BoujeeEnjinia1701/curbcount/cad/drawings/CBC-DWG-101.pdf

### BUILD PLAN SKETCH, PLAN NOT YET BUILT CurbCount · github.com/BoujeeEnjinia1701/curbcount

FRONT VIEW
Scale 1:5; looking at the front (along +Y)

TOP VIEW
Scale 1:5; looking down (along -Z)

RIGHT VIEW
Scale 1:5; looking at the right side (along -X)

160

3 300

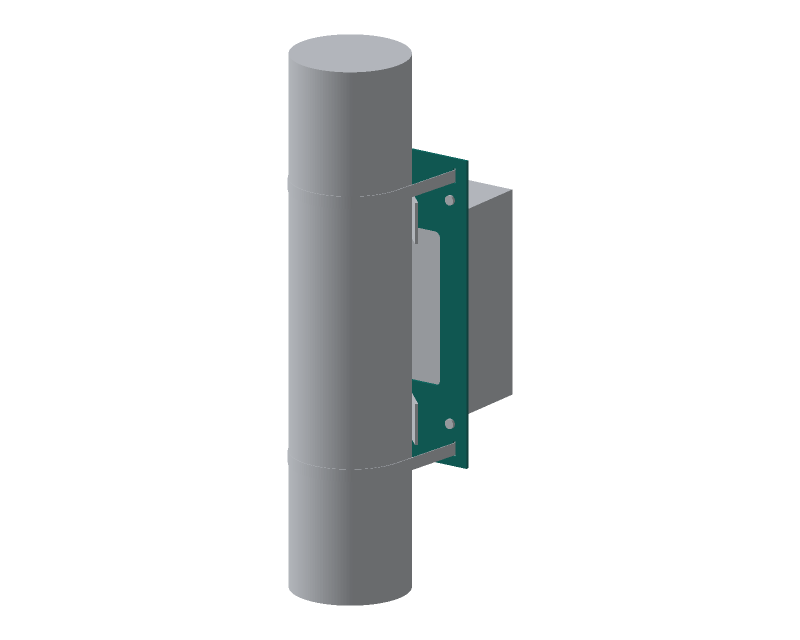
[picture p7: figure]

WHERE IT GOES
This part in colour, its neighbours in grey

HOW TO MAKE IT AND HOW IT FITS
Blank 160 x 300 mm, 3 mm aluminium. Front view is the face the box sits on. Heights from the bottom edge; sideways from the centre line.
Window 100 x 150 mm, 6 mm corners, 75 to 225 mm up: drill the corners 12 mm, cut between with a jigsaw, file straight. It saves weight.
Band slots 3 x 15 mm at 66 mm each side, centred 17 and 283 mm up: chain drill 3 mm and file square. The bands pass through these.
Lug screws 5.5 mm at 62 mm each side, 41 and 259 mm up.
V-saddle screws 4.5 mm on the centre line, 42, 62, 238 and 258 mm up; countersink from the front so the screw heads sit flush.
Deburr every hole and edge; round the corners to about 2 mm.
Fit: V-saddles on the back, the enclosure on the front between the bands; each band crosses the front above or below the box. Check: lay the saddles and lugs on it and look through each hole.
REV | DESCRIPTION | DATE | BY
P1 | Making sketch for the prototype build plan | 2026-10-02 | AC
CURBCOUNT | github.com/BoujeeEnjinia1701/curbcount

## CurbCount enclosure saddle plate: making sketch

DRAWING NO.
CBC-DWG-101

REV
P1

SHEET
1 of 1

SIZE

## ANSI B

SCALE
1:5

UNITS
mm
PROJECTION | DATE
2026-10-02

DRAWN
Amish Chadha

MATERIAL / NOTES
Aluminium sheet 3 mm, 5052 or 6061 class
Licensed CERN-OHL-S-2.0 · Design Molecule Lab · designmolecule.com | Generated from cad/src; do not edit by hand
