BoujeeEnjinia1701/curbcount/cad/drawings/CBC-DWG-102.pdf

### BUILD PLAN SKETCH, PLAN NOT YET BUILT CurbCount · github.com/BoujeeEnjinia1701/curbcount

FRONT VIEW
Scale 1:2; looking at the front (along +Y)

TOP VIEW
Scale 1:2; looking down (along -Z)

RIGHT VIEW
Scale 1:2; looking at the right side (along -X)

49

116 40

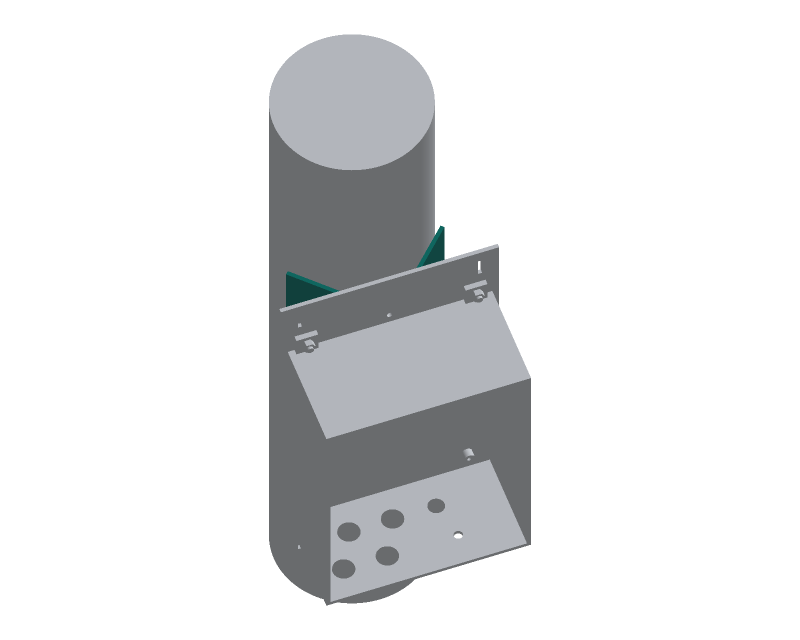
[picture p8: figure]

WHERE IT GOES
This part in colour, its neighbours in grey

HOW TO MAKE IT AND HOW IT FITS
Make four, all the same: two for the enclosure plate, two for the arm plate. Blank 150 x 40 mm of 3 mm sheet: a 20 mm flat in the middle and a
65 mm wing each side. Scribe the two bend lines 10 mm each side
of the centre line.
Bend each wing 45 degrees in a vice with soft jaws, inside radius about 3 mm, so the two wings meet at 90 degrees (the V).
Two holes on the centre line of the flat, 10 mm each side of the middle: drill 3.3 mm and tap M4. File the screw tails flush later. Fit: the flat sits on the back of a saddle plate, the V opens toward the pole; two M4 countersunk screws from the plate's front.
The 114 mm pole touches both wings 43 mm out from the bends; 60 to 140 mm poles also seat on both wings.
Check: both wings at 45 degrees to the flat, within 1 degree.
REV | DESCRIPTION | DATE | BY
P1 | Making sketch for the prototype build plan | 2026-10-02 | AC
CURBCOUNT | github.com/BoujeeEnjinia1701/curbcount

## CurbCount V-saddle (make 4): making sketch

DRAWING NO.
CBC-DWG-102

REV
P1

SHEET
1 of 1

SIZE

## ANSI B

SCALE
1:2

UNITS
mm
PROJECTION | DATE
2026-10-02

DRAWN
Amish Chadha

MATERIAL / NOTES
Aluminium sheet 3 mm, 5052-H32 (bends cold)
Licensed CERN-OHL-S-2.0 · Design Molecule Lab · designmolecule.com | Generated from cad/src; do not edit by hand
