BoujeeEnjinia1701/curbcount/cad/drawings/CBC-DWG-103.pdf

### BUILD PLAN SKETCH, PLAN NOT YET BUILT CurbCount · github.com/BoujeeEnjinia1701/curbcount

FRONT VIEW
Scale 1:5; looking at the front (along +Y)

TOP VIEW
Scale 1:5; looking down (along -Z)

RIGHT VIEW
Scale 1:5; looking at the right side (along -X)

78

150 208

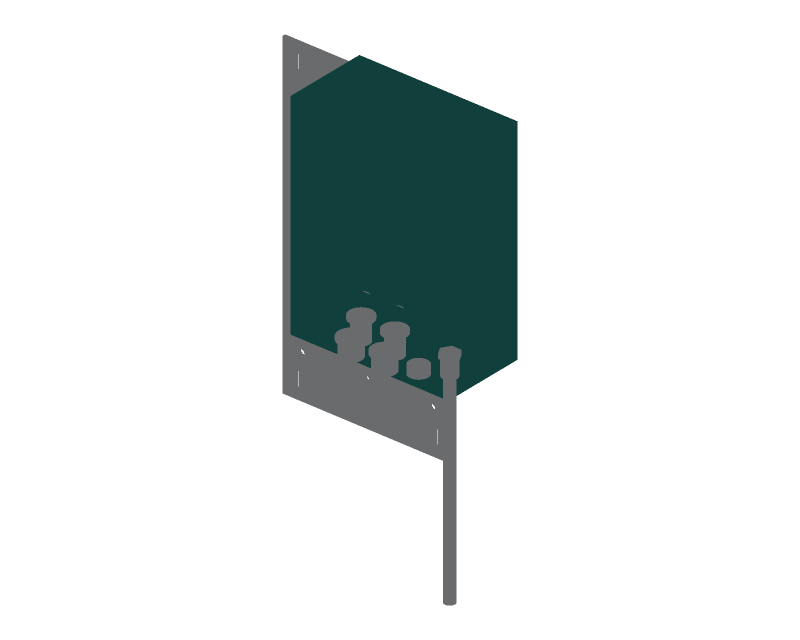
[picture p9: figure]

WHERE IT GOES
This part in colour, its neighbours in grey

HOW TO MAKE IT AND HOW IT FITS
The FieldNode enclosure, drilled exactly as FieldNode's build plan says. Drawn upside down: stand the box on its top, back face toward you. Back row, 27 mm from the back face: gland 1 at 40 left, gland 2 at
8 left (16.2 mm holes), vent at 24 right (12.2 mm).
Front row, 55 mm from the back face: port A at 54 left, port B at
22 left (16.2 mm), antenna at 30 right (6.5 mm).
Left and right as seen from the front (the lid).
Tape the face, pilot drill 3 mm slowly with wood behind, open out with a step drill. No solvents: polycarbonate crazes.
Fit the maker's four lugs at the back corners.
In CurbCount, gland 1 takes the panel lead and port A the sensor cable; gland 2 is plugged and port B capped.
REV | DESCRIPTION | DATE | BY
P1 | Making sketch for the prototype build plan | 2026-10-02 | AC
CURBCOUNT | github.com/BoujeeEnjinia1701/curbcount

## CurbCount FieldNode enclosure: drilling sketch

DRAWING NO.
CBC-DWG-103

REV
P1

SHEET
1 of 1

SIZE

## ANSI B

SCALE
1:5

UNITS
mm
PROJECTION | DATE
2026-10-02

DRAWN
Amish Chadha

MATERIAL / NOTES
Bought IP65 polycarbonate box 150 x 90 x 200 mm
Licensed CERN-OHL-S-2.0 · Design Molecule Lab · designmolecule.com | Generated from cad/src; do not edit by hand
