BoujeeEnjinia1701/curbcount/cad/drawings/CBC-DWG-104.pdf

### BUILD PLAN SKETCH, PLAN NOT YET BUILT CurbCount · github.com/BoujeeEnjinia1701/curbcount

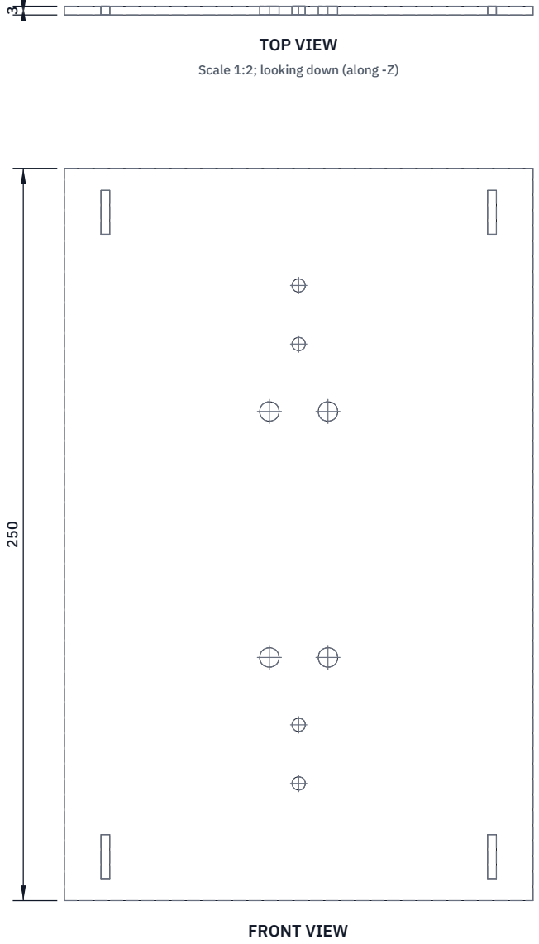
[picture p10: figure]
FRONT VIEW; TOP VIEW; Scale 1:2; looking down (along -Z)

Scale 1:2; looking at the front (along +Y)

RIGHT VIEW
Scale 1:2; looking at the right side (along -X)

160

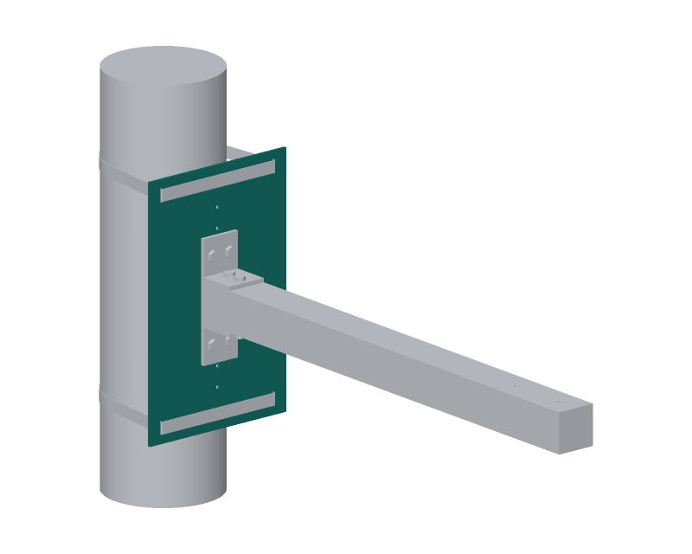
[picture p11: figure]

WHERE IT GOES
This part in colour, its neighbours in grey

HOW TO MAKE IT AND HOW IT FITS
Blank 160 x 250 mm, 3 mm aluminium. Front view is the face the arm butts against. Heights from the bottom edge; sideways from the centre. Band slots 3 x 15 mm at 66 mm each side, centred 15 and 235 mm up: chain drill 3 mm and file square.
Bracket bolts 6.6 mm at 10 mm each side, 83 and 167 mm up. V-saddle screws 4.5 mm on the centre line, 40, 60, 190 and 210 mm up; countersink from the front.
Deburr every hole; round the corners to about 2 mm.
Fit: V-saddles on the back; the arm tube butts the front at mid
height, held by the two brackets; the bands cross the front above and below the brackets.
Check: offer the brackets up and look through the bolt holes.
REV | DESCRIPTION | DATE | BY
P1 | Making sketch for the prototype build plan | 2026-10-02 | AC
CURBCOUNT | github.com/BoujeeEnjinia1701/curbcount

## CurbCount arm saddle plate: making sketch

DRAWING NO.
CBC-DWG-104

REV
P1

SHEET
1 of 1

SIZE

## ANSI B

SCALE
1:2

UNITS
mm
PROJECTION | DATE
2026-10-02

DRAWN
Amish Chadha

MATERIAL / NOTES
Aluminium sheet 3 mm, 5052 or 6061 class
Licensed CERN-OHL-S-2.0 · Design Molecule Lab · designmolecule.com | Generated from cad/src; do not edit by hand
