BoujeeEnjinia1701/curbcount/cad/drawings/CBC-DWG-105.pdf

### BUILD PLAN SKETCH, PLAN NOT YET BUILT CurbCount · github.com/BoujeeEnjinia1701/curbcount

FRONT VIEW
Scale 1:1; looking at the front (along +Y)

TOP VIEW
Scale 1:1; looking down (along -Z)

RIGHT VIEW
Scale 1:1; looking at the right side (along -X)

40

40 40

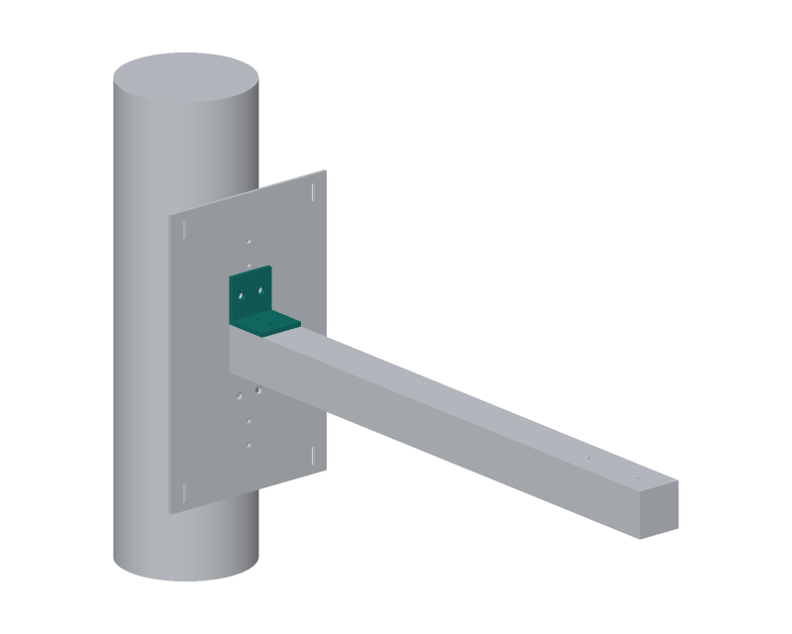
[picture p12: figure]

WHERE IT GOES
This part in colour, its neighbours in grey

HOW TO MAKE IT AND HOW IT FITS
Cut two 40 mm lengths of 40 x 40 x 4 angle; square and deburr. Upright leg (goes on the plate): two 6.6 mm holes 10 mm each side of the middle, 22 mm from the heel (the outside corner).
Flat leg (goes on the tube): two 6.6 mm holes on the middle line, 15 and 30 mm from the heel.
Both brackets are the same; one goes on top of the tube, the other underneath, upside down.
Fit: the upright leg on the plate's front, its heel at the tube's
top (or bottom) face; M6 bolts through the plate, nuts behind. Two M6 bolts go down through both brackets and the tube, each with a crush spacer inside the tube.
Check: the bracket sits flat on both the plate and the tube.
REV | DESCRIPTION | DATE | BY
P1 | Making sketch for the prototype build plan | 2026-10-02 | AC
CURBCOUNT | github.com/BoujeeEnjinia1701/curbcount

## CurbCount arm bracket (make 2): making sketch

DRAWING NO.
CBC-DWG-105

REV
P1

SHEET
1 of 1

SIZE

## ANSI B

SCALE
1:1

UNITS
mm
PROJECTION | DATE
2026-10-02

DRAWN
Amish Chadha

MATERIAL / NOTES
Aluminium equal angle 40 x 40 x 4 mm
Licensed CERN-OHL-S-2.0 · Design Molecule Lab · designmolecule.com | Generated from cad/src; do not edit by hand
