BoujeeEnjinia1701/curbcount/cad/drawings/CBC-DWG-106.pdf

### BUILD PLAN SKETCH, PLAN NOT YET BUILT CurbCount · github.com/BoujeeEnjinia1701/curbcount

FRONT VIEW
Scale 1:5; looking at the front (along +Y)

TOP VIEW
Scale 1:5; looking down (along -Z)

RIGHT VIEW
Scale 1:5; looking at the right side (along -X)

498

40 40

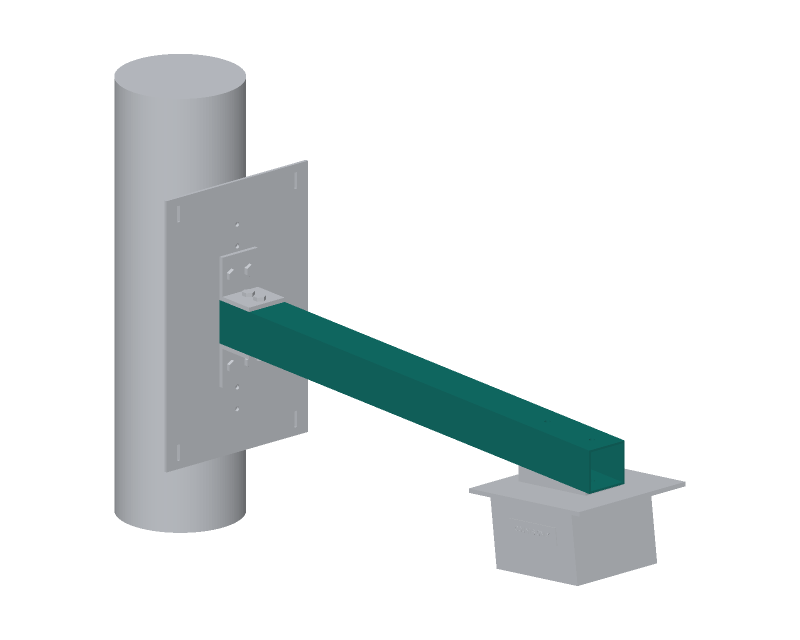
[picture p13: figure]

WHERE IT GOES
This part in colour, its neighbours in grey

HOW TO MAKE IT AND HOW IT FITS
Cut 498 mm of 40 x 40 x 2 tube; square both ends (the pole end must sit flat on the plate) and deburr.
Plate end: two 6.6 mm holes straight through top and bottom walls, on the centre line, 15 and 30 mm from the end.
Head end: two 5.5 mm holes straight through, on the centre line, 418 and 478 mm from the plate end.
Drill each pair square through both walls (drill press, V-block).
Cut four crush spacers 36 mm long from 10 mm aluminium tube; they sit inside the tube on the bolts so the walls do not crush.
Fit a plastic end cap in the head end.
Check: on a flat bench the tube does not rock; holes line up
top to bottom (a rod passes straight through).
REV | DESCRIPTION | DATE | BY
P1 | Making sketch for the prototype build plan | 2026-10-02 | AC
CURBCOUNT | github.com/BoujeeEnjinia1701/curbcount

## CurbCount arm tube: making sketch

DRAWING NO.
CBC-DWG-106

REV
P1

SHEET
1 of 1

SIZE

## ANSI B

SCALE
1:5

UNITS
mm
PROJECTION | DATE
2026-10-02

DRAWN
Amish Chadha

MATERIAL / NOTES
Aluminium square tube 40 x 40 x 2 mm, 6063
Licensed CERN-OHL-S-2.0 · Design Molecule Lab · designmolecule.com | Generated from cad/src; do not edit by hand
