BoujeeEnjinia1701/curbcount/cad/drawings/CBC-DWG-107.pdf

### BUILD PLAN SKETCH, PLAN NOT YET BUILT CurbCount · github.com/BoujeeEnjinia1701/curbcount

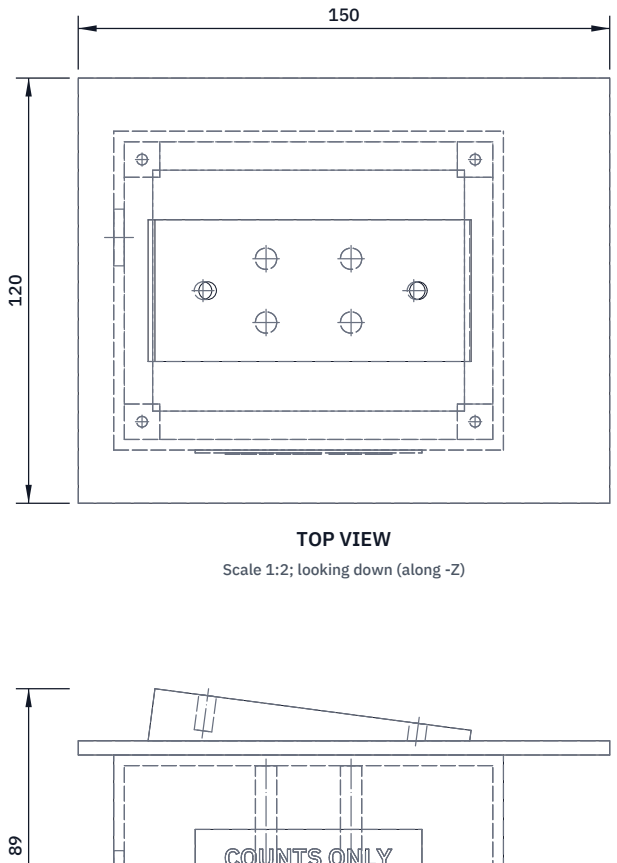
[picture p14: figure]
TOP VIEW; Scale 1:2; looking down (along -Z)

FRONT VIEW
Scale 1:2; looking at the front (along +Y)

RIGHT VIEW
Scale 1:2; looking at the right side (along -X)

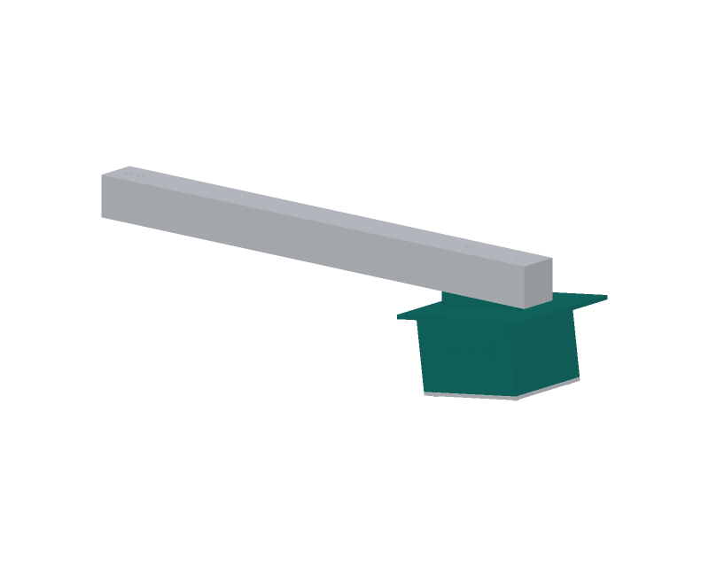
[picture p15: figure]

WHERE IT GOES
This part in colour, its neighbours in grey

HOW TO MAKE IT AND HOW IT FITS
Print in ASA in an enclosed printer, hood down on the bed; support the window ledge. Housing 110 x 90 x 70 mm, walls 3 mm,
hood 150 x 120 x 4 mm, set 10 mm toward the road side.
Ledge 8 mm wide inside the open bottom: the window clamps to it. Four corner bosses: press in M3 heat-set inserts, 47 and 37 mm each side of centre, from below.
Four standoffs from the roof carry the array breakout.
Wedge pad on the hood top: it makes the 7.5 degree tilt; its top is level under the arm. Press in two M5 heat-set inserts, 60 apart. End wall (pole side): 16.2 mm hole, 15 mm off centre, for the gland. Drill a 5 mm lanyard hole in the hood's road-side overhang. Road-side wall: a raised plaque 64 x 16 mm, 0.8 mm high, with COUNTS ONLY in 7 mm letters 0.4 mm higher, printed in the housing. Check: the wedge top is flat; the ledge face is flat for the film.
REV | DESCRIPTION | DATE | BY
P1 | Making sketch for the prototype build plan | 2026-10-02 | AC
CURBCOUNT | github.com/BoujeeEnjinia1701/curbcount

## CurbCount head housing: making sketch

DRAWING NO.
CBC-DWG-107

REV
P1

SHEET
1 of 1

SIZE

## ANSI B

SCALE
1:2

UNITS
mm
PROJECTION | DATE
2026-10-02

DRAWN
Amish Chadha

MATERIAL / NOTES
ASA, 3D printed, 4 perimeters, 40 % infill
Licensed CERN-OHL-S-2.0 · Design Molecule Lab · designmolecule.com | Generated from cad/src; do not edit by hand
