BoujeeEnjinia1701/curbcount/cad/drawings/CBC-DWG-108.pdf

### BUILD PLAN SKETCH, PLAN NOT YET BUILT CurbCount · github.com/BoujeeEnjinia1701/curbcount

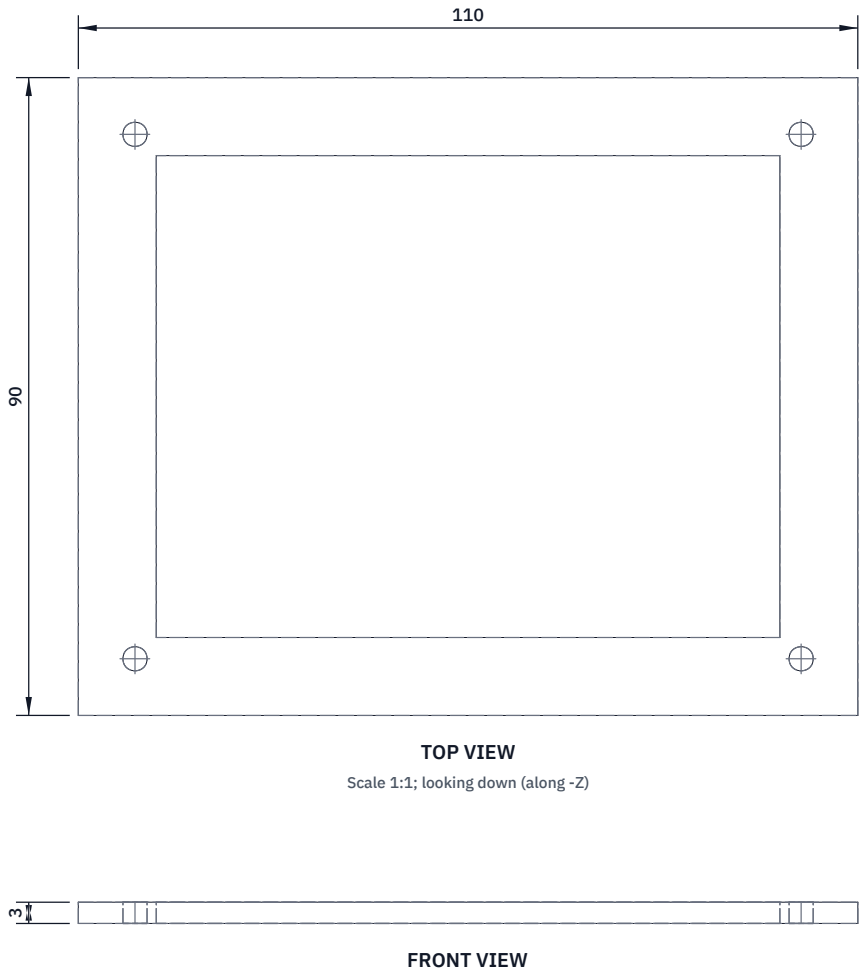
[picture p16: figure]
FRONT VIEW; TOP VIEW; Scale 1:1; looking down (along -Z)

Scale 1:1; looking at the front (along +Y)

RIGHT VIEW
Scale 1:1; looking at the right side (along -X)

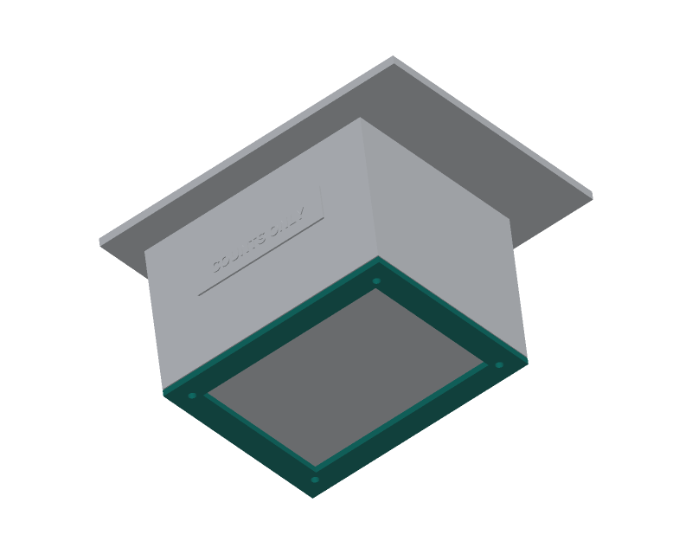
[picture p17: figure]

WHERE IT GOES
This part in colour, its neighbours in grey

HOW TO MAKE IT AND HOW IT FITS
Frame: print flat in ASA, 110 x 90 x 3 mm with an 88 x 68 mm opening and four 3.4 mm holes, 47 and 37 mm each side of centre.
Film: cut 100 x 80 mm from 0.5 mm unpigmented HDPE with a sharp knife on glass; do not touch the middle with bare fingers.
Use the frame as a template: punch four 3.5 mm holes in the film. Fit: film on the housing ledge, frame over it, four M3 screws into
the heat-set inserts, tightened evenly until the film is flat.
The array looks through the 88 x 68 mm opening; the field of view needs only about 30 x 20 mm of it.
Check: the film is flat and taut with no creases in the opening.
REV | DESCRIPTION | DATE | BY
P1 | Making sketch for the prototype build plan | 2026-10-02 | AC
CURBCOUNT | github.com/BoujeeEnjinia1701/curbcount

## CurbCount window frame and film: making sketch

DRAWING NO.
CBC-DWG-108

REV
P1

SHEET
1 of 1

SIZE

## ANSI B

SCALE
1:1

UNITS
mm
PROJECTION | DATE
2026-10-02

DRAWN
Amish Chadha

MATERIAL / NOTES
Frame ASA, 3D printed; film 0.5 mm HDPE
Licensed CERN-OHL-S-2.0 · Design Molecule Lab · designmolecule.com | Generated from cad/src; do not edit by hand
