BoujeeEnjinia1701/curbcount/cad/drawings/CBC-DWG-109.pdf

### BUILD PLAN SKETCH, PLAN NOT YET BUILT CurbCount · github.com/BoujeeEnjinia1701/curbcount

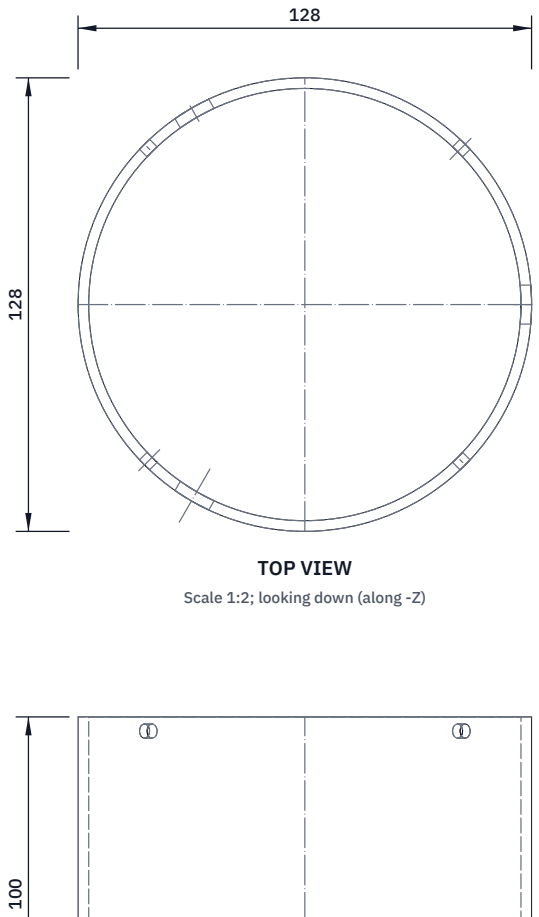
[picture p18: figure]
TOP VIEW; Scale 1:2; looking down (along -Z)

FRONT VIEW
Scale 1:2; looking at the front (along +Y)

RIGHT VIEW
Scale 1:2; looking at the right side (along -X)

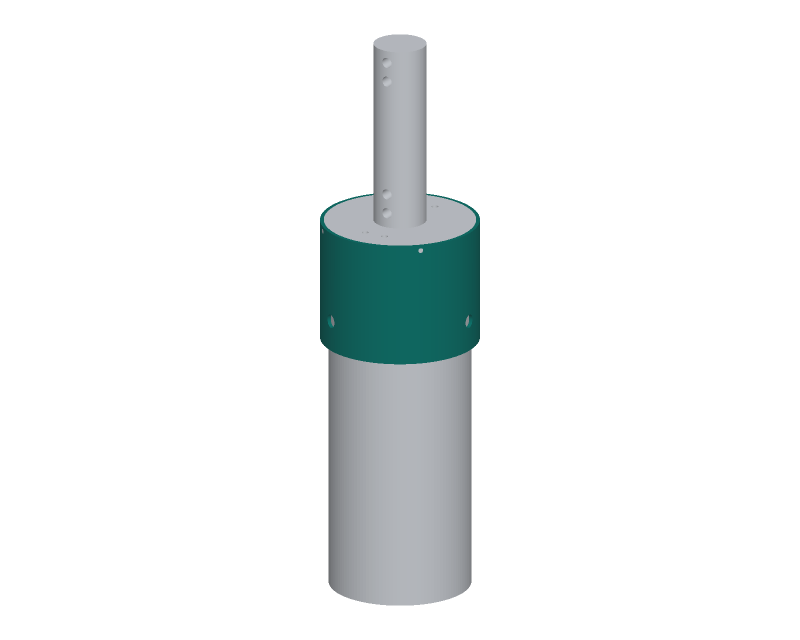
[picture p19: figure]

WHERE IT GOES
This part in colour, its neighbours in grey

HOW TO MAKE IT AND HOW IT FITS
Cut 100 mm of round tube; square and deburr both ends.
The bore must be 122 mm or more so it slides over a 114 mm pole. Top: four 4.5 mm holes 4 mm down from the top edge, at 45, 135, 225 and 315 degrees; countersink them for M4 screws.
Bottom: three 11 mm holes 25 mm up from the bottom edge, at 0, 120 and 240 degrees; set an M8 stainless rivet nut in each.
Put the hole at 0 degrees on the road side when fitting.
Fit: the cap disc goes inside the top, flush, on the four radial
screws; the sleeve then sits on the pole top through the disc.
Three M8 cup-point set screws in the rivet nuts centre it on the pole. Check: it slides over a 114 mm tube with 3 to 4 mm all round.
REV | DESCRIPTION | DATE | BY
P1 | Making sketch for the prototype build plan | 2026-10-02 | AC
CURBCOUNT | github.com/BoujeeEnjinia1701/curbcount

## CurbCount sleeve: making sketch

DRAWING NO.
CBC-DWG-109

REV
P1

SHEET
1 of 1

SIZE

## ANSI B

SCALE
1:2

UNITS
mm
PROJECTION | DATE
2026-10-02

DRAWN
Amish Chadha

MATERIAL / NOTES
Aluminium round tube about 128 x 3 mm, bore 122 mm or more
Licensed CERN-OHL-S-2.0 · Design Molecule Lab · designmolecule.com | Generated from cad/src; do not edit by hand
