BoujeeEnjinia1701/curbcount/cad/drawings/CBC-DWG-110.pdf

### BUILD PLAN SKETCH, PLAN NOT YET BUILT CurbCount · github.com/BoujeeEnjinia1701/curbcount

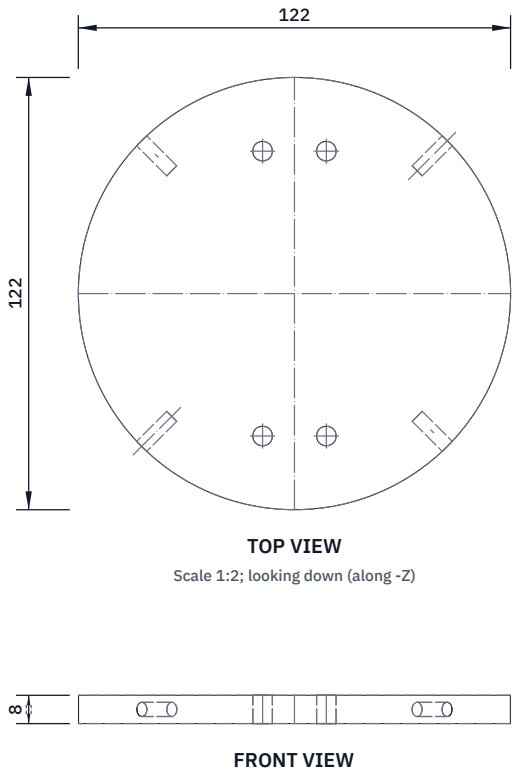
[picture p20: figure]
FRONT VIEW; TOP VIEW; Scale 1:2; looking down (along -Z)

Scale 1:2; looking at the front (along +Y)

RIGHT VIEW
Scale 1:2; looking at the right side (along -X)

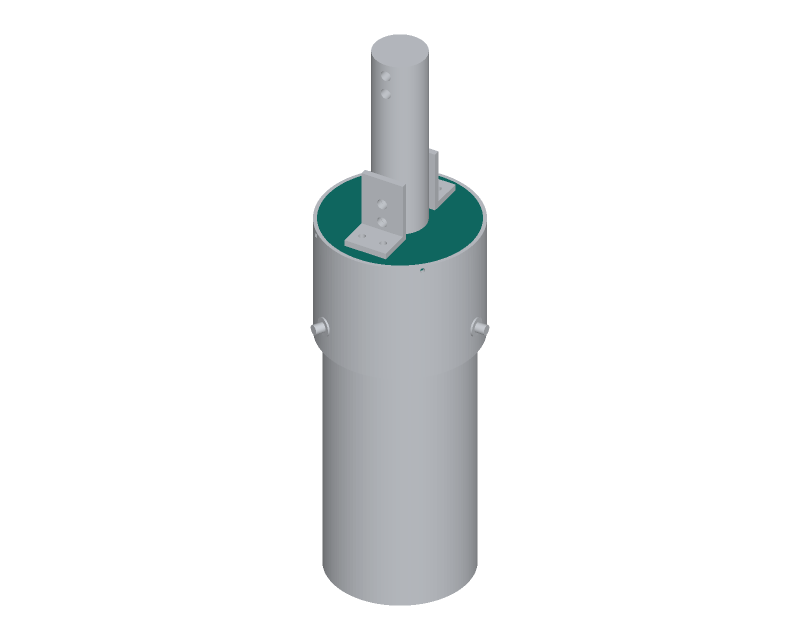
[picture p21: figure]

WHERE IT GOES
This part in colour, its neighbours in grey

HOW TO MAKE IT AND HOW IT FITS
Cut a disc 122 mm across from 8 mm plate (hole saw or bandsaw and file); it must be a close sliding fit in the sleeve bore.
Edge: four holes into the edge at 45, 135, 225 and 315 degrees,
4 mm from the top face: drill 3.3 mm 12 deep and tap M4.
Drill them through the sleeve's holes with the disc in place.
Face: eight 5.5 mm holes for the lower clips, 40 mm each side of the centre line and 9 mm either side of the cross line; countersink
them from below so the screw heads sit flush (the pole top bears on the underside).
Fit: disc inside the top of the sleeve, top faces flush.
Check: underside flat; no screw head stands proud.
REV | DESCRIPTION | DATE | BY
P1 | Making sketch for the prototype build plan | 2026-10-02 | AC
CURBCOUNT | github.com/BoujeeEnjinia1701/curbcount

## CurbCount cap disc: making sketch

DRAWING NO.
CBC-DWG-110

REV
P1

SHEET
1 of 1

SIZE

## ANSI B

SCALE
1:2

UNITS
mm
PROJECTION | DATE
2026-10-02

DRAWN
Amish Chadha

MATERIAL / NOTES
Aluminium plate 8 mm, 6082 or 5083 class
Licensed CERN-OHL-S-2.0 · Design Molecule Lab · designmolecule.com | Generated from cad/src; do not edit by hand
