BoujeeEnjinia1701/curbcount/cad/drawings/CBC-DWG-111.pdf

### BUILD PLAN SKETCH, PLAN NOT YET BUILT CurbCount · github.com/BoujeeEnjinia1701/curbcount

FRONT VIEW
Scale 1:2; looking at the front (along +Y)

TOP VIEW
Scale 1:2; looking down (along -Z)

RIGHT VIEW
Scale 1:2; looking at the right side (along -X)

42

42 150

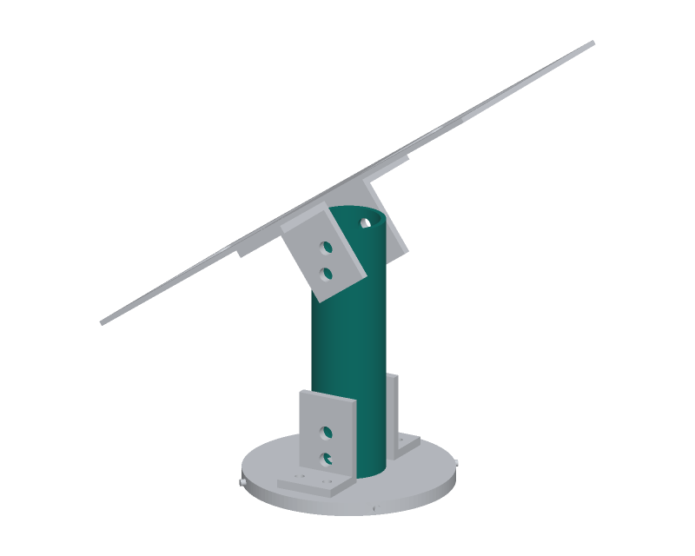
[picture p22: figure]

WHERE IT GOES
This part in colour, its neighbours in grey

HOW TO MAKE IT AND HOW IT FITS
Cut 150 mm of 42.4 x 3.0 tube; square both ends and deburr. Fit a plug in each end first (next sheet), then drill the post and plug together, straight across, 8.5 mm:
bottom end: 12 and 28 mm up from the bottom;
top end: 10 and 26 mm down from the top.
All four holes lie in one plane: drill in a V-block on a drill press. Fit: the bottom end stands on the cap disc between the lower clips; the top end sits between the upper clips under the rail plate,
4 mm clear of it. Two M8 bolts through each end.
Check: a rod passes straight through each hole pair.
REV | DESCRIPTION | DATE | BY
P1 | Making sketch for the prototype build plan | 2026-10-02 | AC
CURBCOUNT | github.com/BoujeeEnjinia1701/curbcount

## CurbCount post: making sketch

DRAWING NO.
CBC-DWG-111

REV
P1

SHEET
1 of 1

SIZE

## ANSI B

SCALE
1:2

UNITS
mm
PROJECTION | DATE
2026-10-02

DRAWN
Amish Chadha

MATERIAL / NOTES
Aluminium round tube 42.4 x 3.0 mm, 6063
Licensed CERN-OHL-S-2.0 · Design Molecule Lab · designmolecule.com | Generated from cad/src; do not edit by hand
