BoujeeEnjinia1701/curbcount/cad/drawings/CBC-DWG-113.pdf

### BUILD PLAN SKETCH, PLAN NOT YET BUILT CurbCount · github.com/BoujeeEnjinia1701/curbcount

FRONT VIEW
Scale 1:1; looking at the front (along +Y)

TOP VIEW
Scale 1:1; looking down (along -Z)

RIGHT VIEW
Scale 1:1; looking at the right side (along -X)

35

30 50

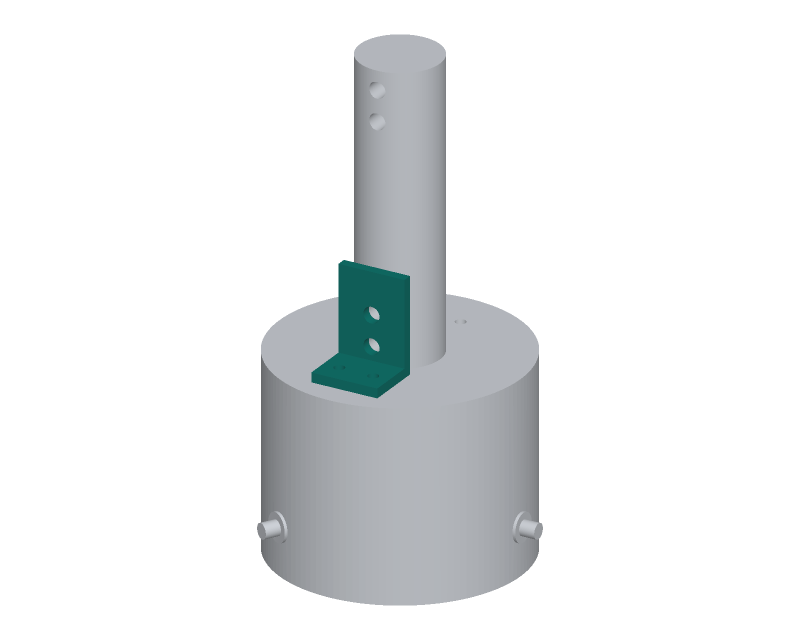
[picture p23: figure]

WHERE IT GOES
This part in colour, its neighbours in grey

HOW TO MAKE IT AND HOW IT FITS
Cut two 35 mm lengths of 50 x 50 x 5 angle.
Trim the flat leg to 30 mm wide (from the heel) so it fits on the disc. Upright leg: two 8.5 mm holes at mid-length, 12 and 28 mm up from the bottom face of the flat leg.
Flat leg: two 5.5 mm holes 19 mm out from the upright leg's inside face, 9 mm either side of mid-length.
Both clips are the same; they face each other across the post. Fit: flat leg on the disc, upright leg against the post; two M5 countersunk screws up through the disc, nuts on top.
Check: the clips stand square on the disc, 42.4 mm apart inside.
REV | DESCRIPTION | DATE | BY
P1 | Making sketch for the prototype build plan | 2026-10-02 | AC
CURBCOUNT | github.com/BoujeeEnjinia1701/curbcount

## CurbCount lower post clip (make 2): making sketch

DRAWING NO.
CBC-DWG-113

REV
P1

SHEET
1 of 1

SIZE

## ANSI B

SCALE
1:1

UNITS
mm
PROJECTION | DATE
2026-10-02

DRAWN
Amish Chadha

MATERIAL / NOTES
Aluminium equal angle 50 x 50 x 5 mm
Licensed CERN-OHL-S-2.0 · Design Molecule Lab · designmolecule.com | Generated from cad/src; do not edit by hand
