BoujeeEnjinia1701/curbcount/cad/drawings/CBC-DWG-114.pdf

### BUILD PLAN SKETCH, PLAN NOT YET BUILT CurbCount · github.com/BoujeeEnjinia1701/curbcount

FRONT VIEW
Scale 1:1; looking at the front (along +Y)

TOP VIEW
Scale 1:1; looking down (along -Z)

RIGHT VIEW
Scale 1:1; looking at the right side (along -X)

35

50 50

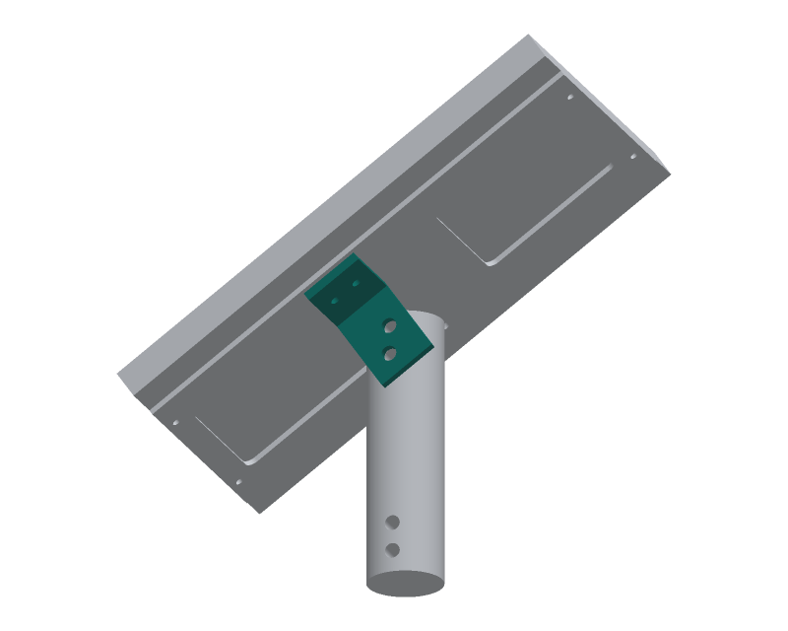
[picture p24: figure]

WHERE IT GOES
This part in colour, its neighbours in grey

HOW TO MAKE IT AND HOW IT FITS
Cut two 35 mm lengths of 50 x 50 x 5 angle.
Flat leg (goes under the rail plate): two 5.5 mm holes 30 mm out from the upright leg's inside face, 10 and 25 mm from one end. Upright leg: two 8.5 mm holes for the post bolts. Mark them from
the post: clamp the clip to the rail plate, set the post between
the clips at the 35 degree tilt, and drill through the post holes.
They fall about 12 and 21 mm from the upper end, 25 and 38 mm down. The two clips are mirror images; drill them as a pair.
Fit: M5 screws through the rail plate, nuts under the clip.
This joint sets the panel's 35 degree tilt.
Check: the rail plate sits at 35 degrees, give or take 1.
REV | DESCRIPTION | DATE | BY
P1 | Making sketch for the prototype build plan | 2026-10-02 | AC
CURBCOUNT | github.com/BoujeeEnjinia1701/curbcount

## CurbCount upper post clip (make 2): making sketch

DRAWING NO.
CBC-DWG-114

REV
P1

SHEET
1 of 1

SIZE

## ANSI B

SCALE
1:1

UNITS
mm
PROJECTION | DATE
2026-10-02

DRAWN
Amish Chadha

MATERIAL / NOTES
Aluminium equal angle 50 x 50 x 5 mm
Licensed CERN-OHL-S-2.0 · Design Molecule Lab · designmolecule.com | Generated from cad/src; do not edit by hand
