BoujeeEnjinia1701/curbcount/cad/drawings/CBC-DWG-115.pdf

### BUILD PLAN SKETCH, PLAN NOT YET BUILT CurbCount · github.com/BoujeeEnjinia1701/curbcount

FRONT VIEW
Scale 1:5; looking at the front (along +Y)

TOP VIEW
Scale 1:5; looking down (along -Z)

RIGHT VIEW
Scale 1:5; looking at the right side (along -X)

290

150 3

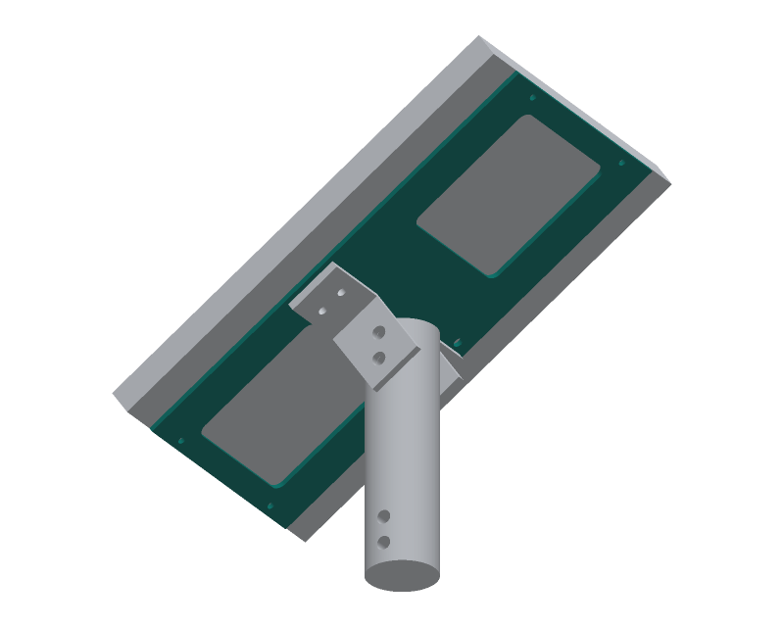
[picture p25: figure]

WHERE IT GOES
This part in colour, its neighbours in grey

HOW TO MAKE IT AND HOW IT FITS
Blank 290 x 150 mm of 3 mm sheet; the long side runs up the slope. Lip bolts: four 4.5 mm holes 6 mm in from each short end, 50 mm each side of the centre line (they go through the panel's lip).
Clip screws: four 5.5 mm holes, 51 mm each side of the centre line, 15 and 30 mm below the middle (toward the low edge).
Two lightening windows 90 x 90 mm, 6 mm corners, centred 85 mm each side of the middle along the long side.
Lanyard hole 6 mm on the middle line, 12 mm in from one long edge. Deburr everything.
Fit: the panel's frame lip sits on the plate's ends; M4 bolts with
the nuts inside the frame. The upper clips go underneath.
Check: the panel lip holes line up with the plate's end holes.
REV | DESCRIPTION | DATE | BY
P1 | Making sketch for the prototype build plan | 2026-10-02 | AC
CURBCOUNT | github.com/BoujeeEnjinia1701/curbcount

## CurbCount rail plate: making sketch

DRAWING NO.
CBC-DWG-115

REV
P1

SHEET
1 of 1

SIZE

## ANSI B

SCALE
1:5

UNITS
mm
PROJECTION | DATE
2026-10-02

DRAWN
Amish Chadha

MATERIAL / NOTES
Aluminium sheet 3 mm, 5052 or 6061 class
Licensed CERN-OHL-S-2.0 · Design Molecule Lab · designmolecule.com | Generated from cad/src; do not edit by hand
