BoujeeEnjinia1701/curbcount/cad/drawings/CBC-DWG-116.pdf

### BUILD PLAN SKETCH, PLAN NOT YET BUILT CurbCount · github.com/BoujeeEnjinia1701/curbcount

FRONT VIEW
Scale 1:2; looking at the front (along +Y)

TOP VIEW
Scale 1:2; looking down (along -Z)

RIGHT VIEW
Scale 1:2; looking at the right side (along -X)

150

2 200

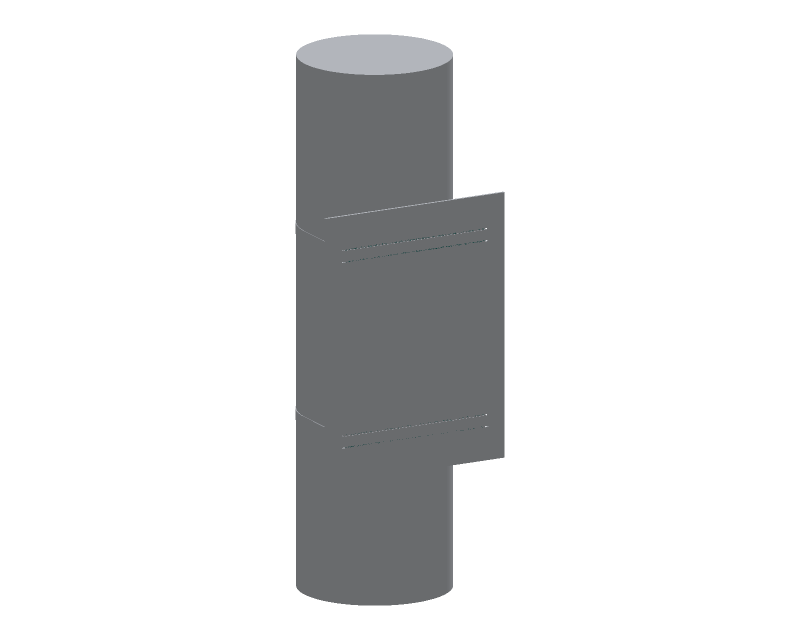
[picture p26: figure]

WHERE IT GOES
This part in colour, its neighbours in grey

HOW TO MAKE IT AND HOW IT FITS
Blank 150 x 200 mm of 2 mm aluminium; round the corners 5 mm. Four tie slots 3 x 10 mm, 60 mm each side of the centre line, centred 30 and 170 mm up from the bottom edge.
Print or apply a UV-stable face: what is counted, "No images are stored or sent; only counts leave the device", and the repository link. Fit: the back lies against the pole, centred on it; two stainless
steel cable ties pass round the pole and through the slots.
At the site it goes at eye height, about 2.6 m up, facing the
sidewalk.
Check: the ties pull the plate flat against the pole.
REV | DESCRIPTION | DATE | BY
P1 | Making sketch for the prototype build plan | 2026-10-02 | AC
CURBCOUNT | github.com/BoujeeEnjinia1701/curbcount

## CurbCount public notice plate: making sketch

DRAWING NO.
CBC-DWG-116

REV
P1

SHEET
1 of 1

SIZE

## ANSI B

SCALE
1:2

UNITS
mm
PROJECTION | DATE
2026-10-02

DRAWN
Amish Chadha

MATERIAL / NOTES
Aluminium sheet 2 mm, printed UV-stable face
Licensed CERN-OHL-S-2.0 · Design Molecule Lab · designmolecule.com | Generated from cad/src; do not edit by hand
