BoujeeEnjinia1701/curbcount/cad/drawings/CBC-DWG-001.png

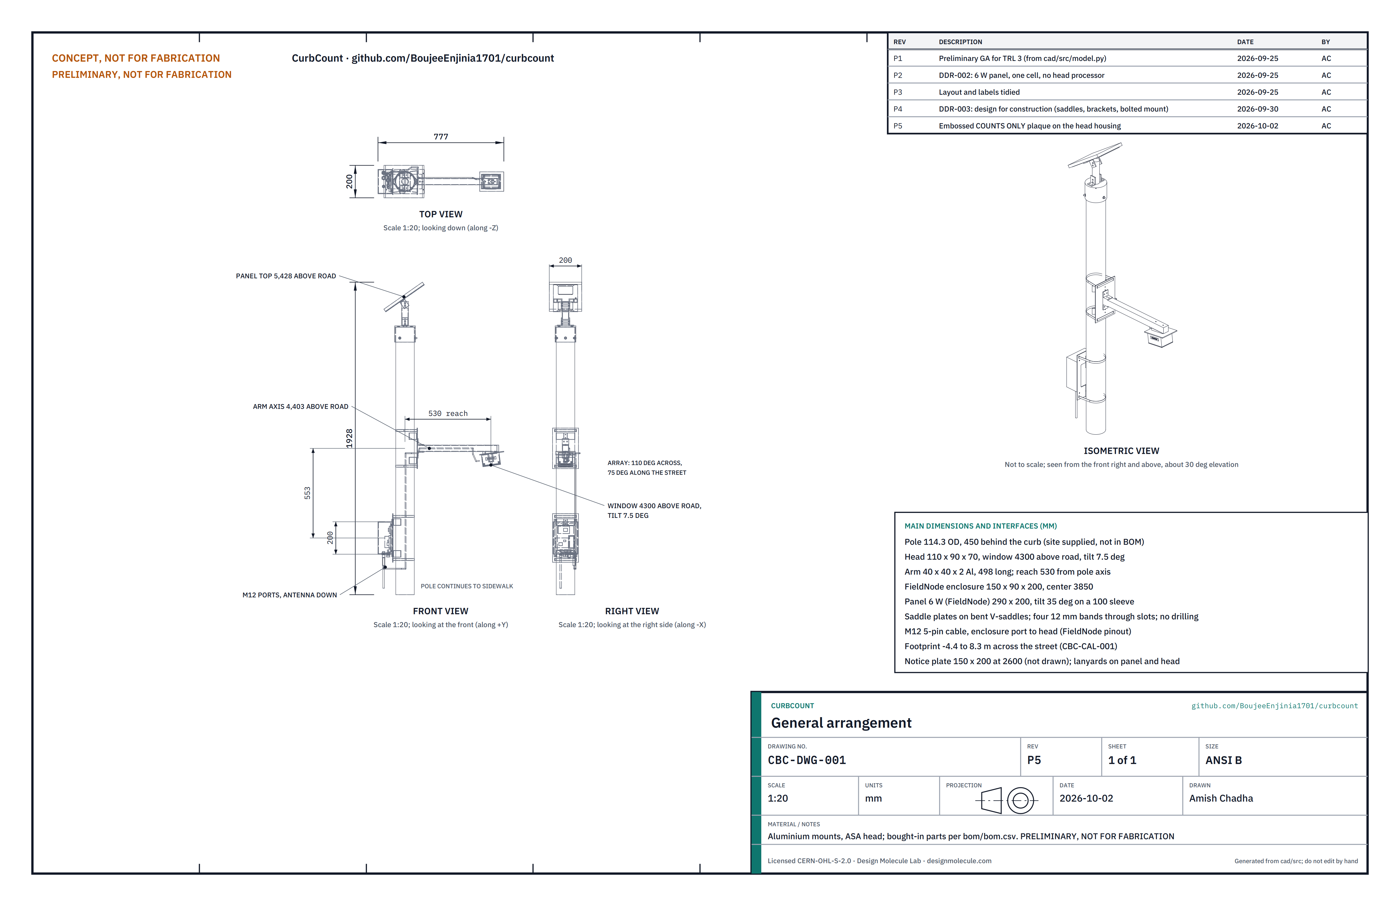
cad/drawings/CBC-DWG-001.png
