BoujeeEnjinia1701/curbcount/media/card.png

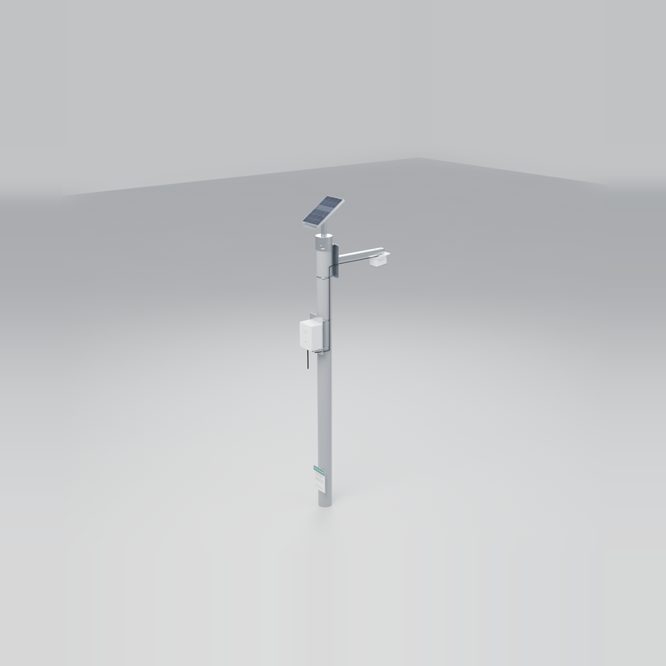
media/card.png
