BoujeeEnjinia1701/curbcount/media/concept-blueprint.png

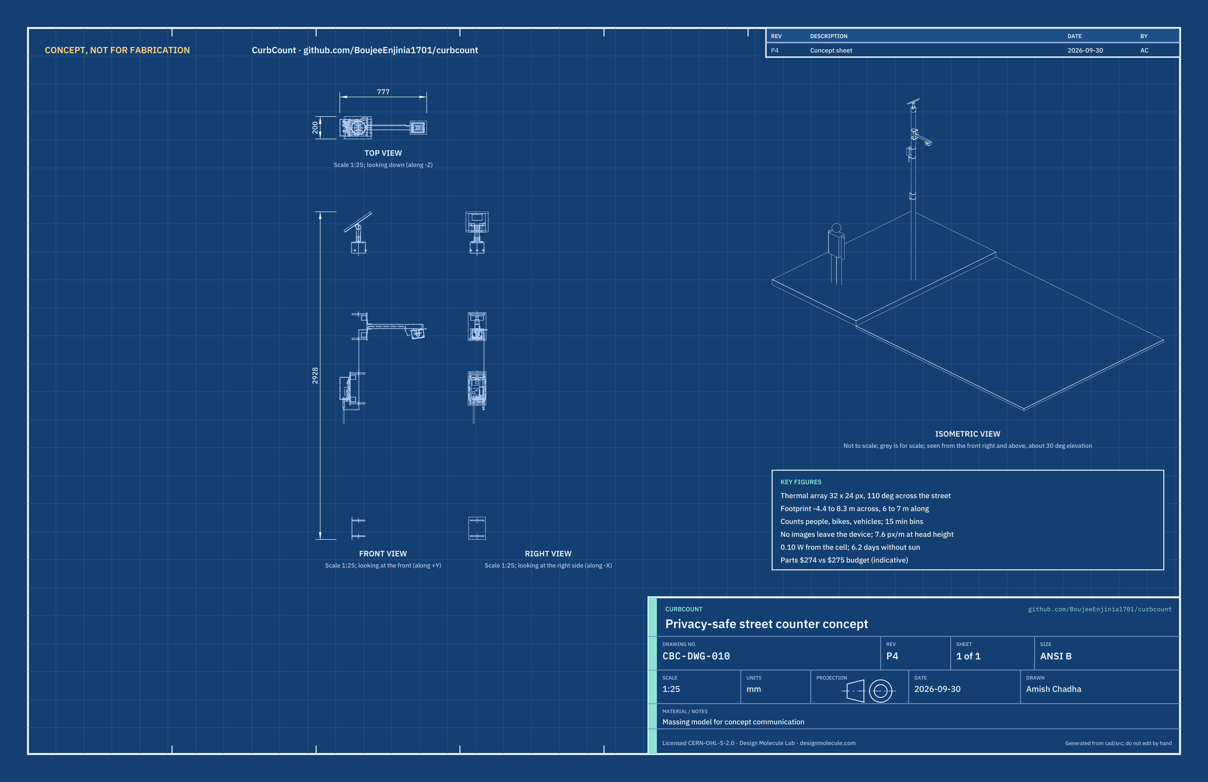
media/concept-blueprint.png
