BoujeeEnjinia1701/curbcount/media/render-detail.png

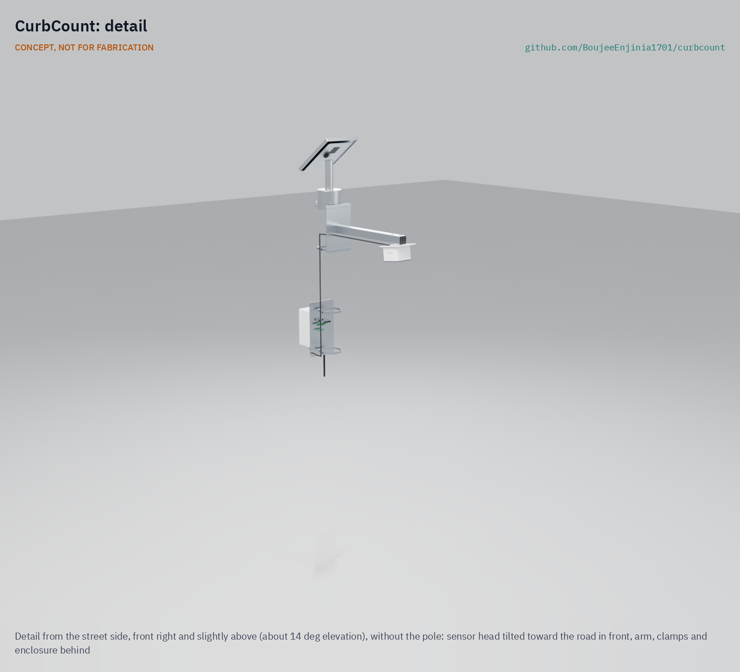
media/render-detail.png
