BoujeeEnjinia1701/curbcount/media/render-exploded.png

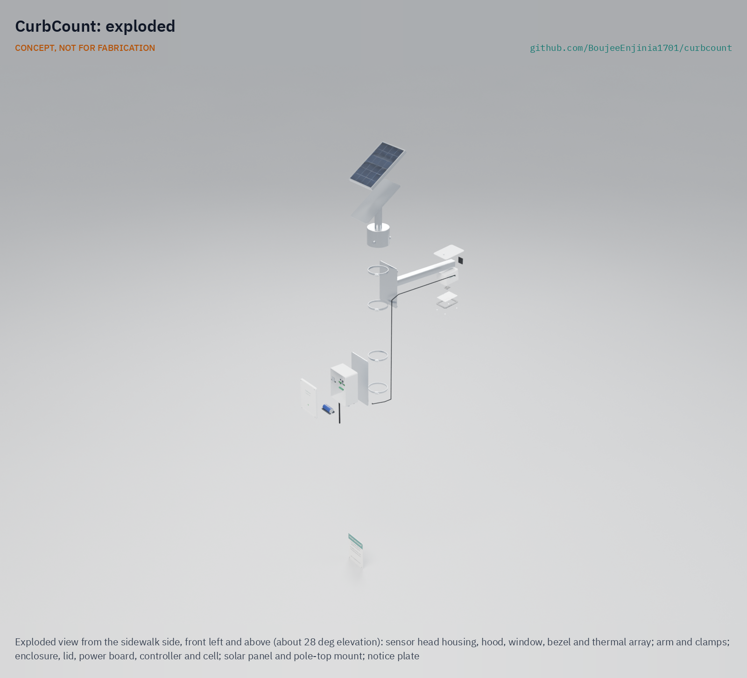
media/render-exploded.png
