BoujeeEnjinia1701/curbcount/media/social-preview.png

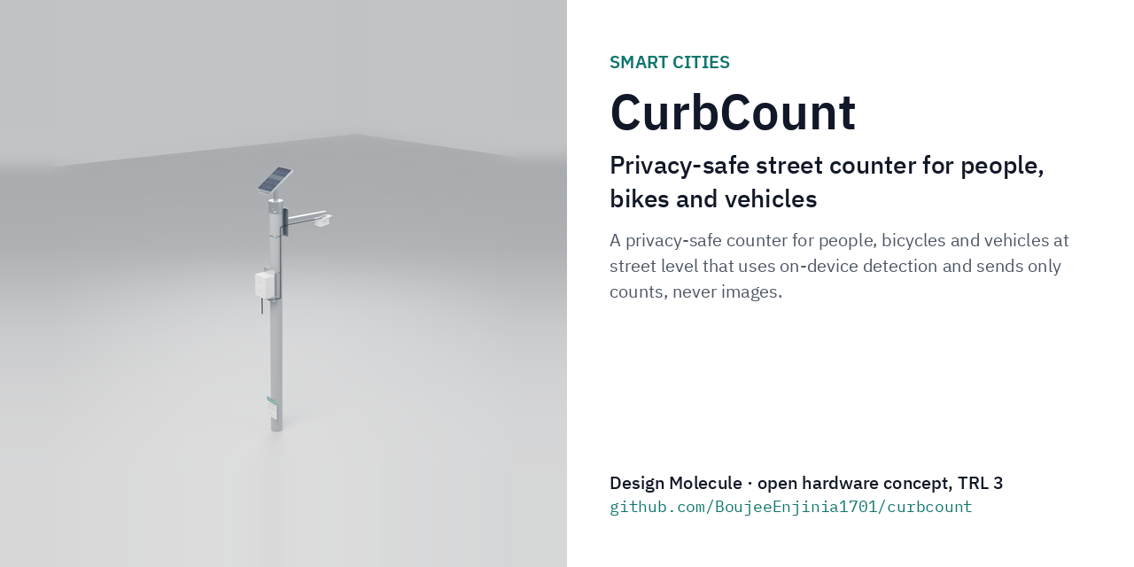
media/social-preview.png
