BoujeeEnjinia1701/curbcount/cad/drawings/CBC-DWG-112.pdf

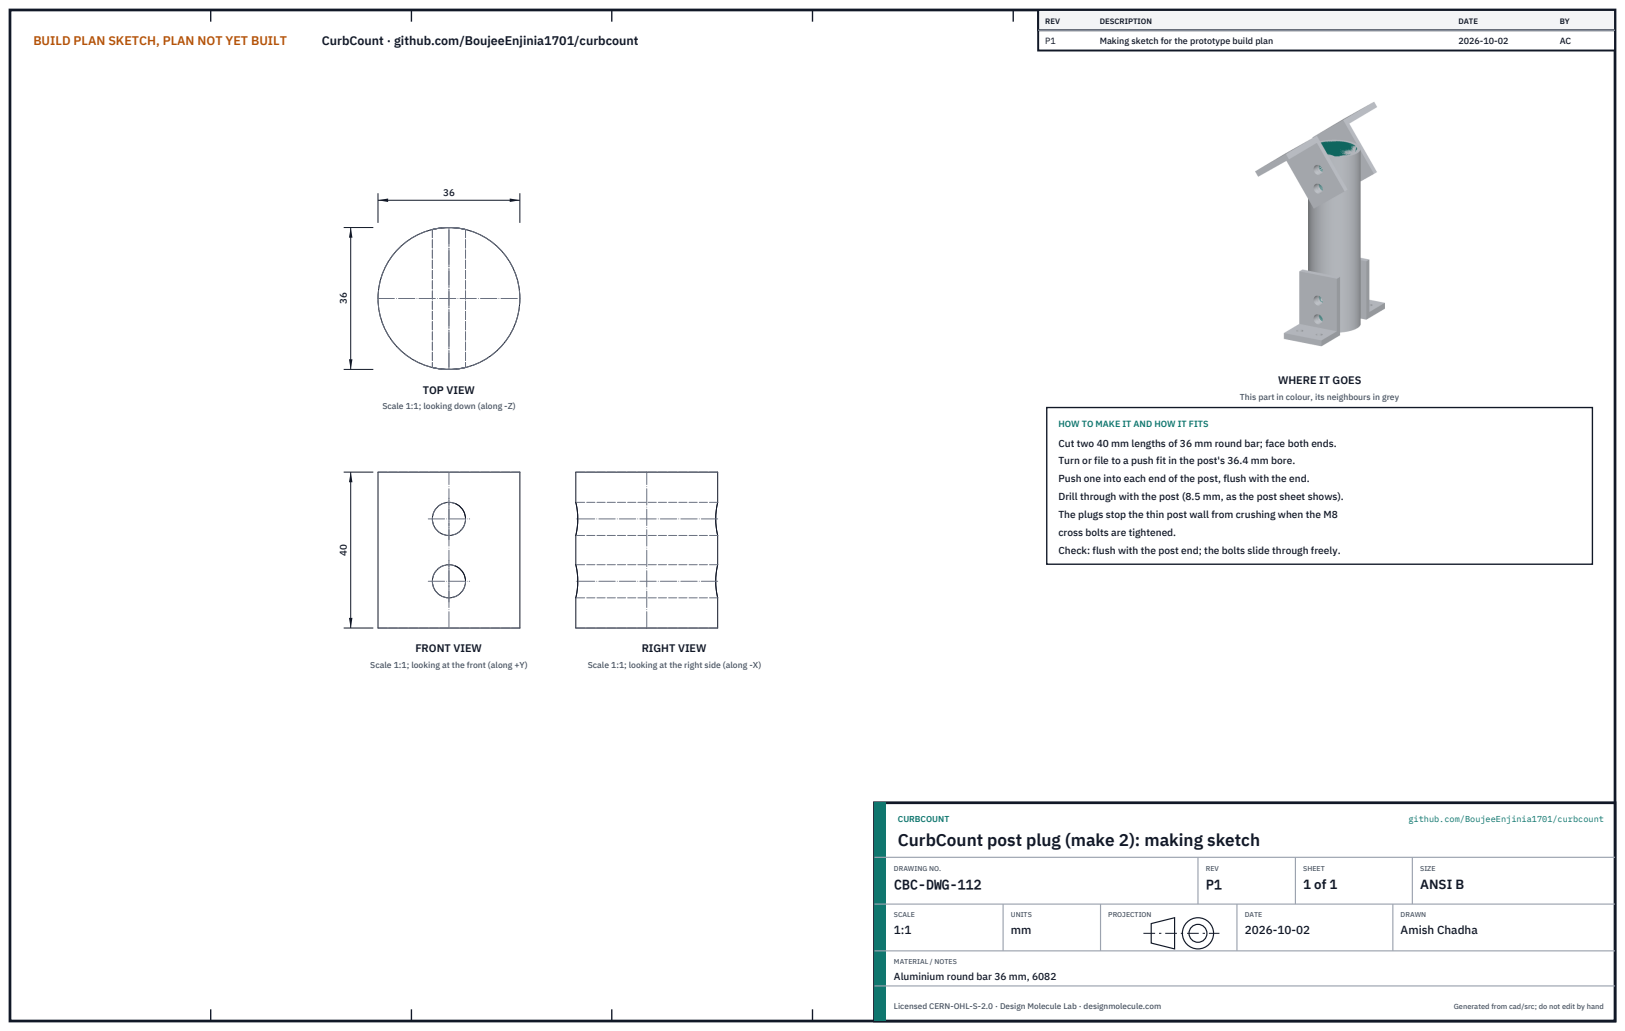
[picture p113: page 1]
BUILD PLAN SKETCH, PLAN NOT YET BUILT; CurbCount · github.com/BoujeeEnjinia1701/curbcount; FRONT VIEW; TOP VIEW; RIGHT VIEW; REV; DESCRIPTION; DATE; Making sketch for the prototype build plan; CURBCOUNT; github.com/BoujeeEnjinia1701/curbcount; DRAWING NO. CBC-DWG-112; REV P1; SHEET 1 of 1; SIZE ANSI B; SCALE 1:1; UNITS mm; PROJECTION; DRAWN Amish Chadha; Licensed CERN-OHL-S-2.0 · Design Molecule Lab · designmolecule.com; Generated from cad/src; do not edit by hand

WHERE IT GOES

This part in colour, its neighbours in grey

Scale 1:1; looking down (along -Z)

HOW TO MAKE IT AND HOW IT FITS
Cut two 40 mm lengths of 36 mm round bar; face both ends.
Turn or file to a push fit in the post's 36.4 mm bore.
Push one into each end of the post, flush with the end.
Drill through with the post (8.5 mm, as the post sheet shows).
The plugs stop the thin post wall from crushing when the M8
cross bolts are tightened.
Check: flush with the post end; the bolts slide through freely.

Scale 1:1; looking at the front (along +Y)

Scale 1:1; looking at the right side (along -X)

CurbCount post plug (make 2): making sketch

MATERIAL / NOTES
Aluminium round bar 36 mm, 6082
